Ninjago77/night_light_madness/images/Screenshot 2026-06-29 014659.png

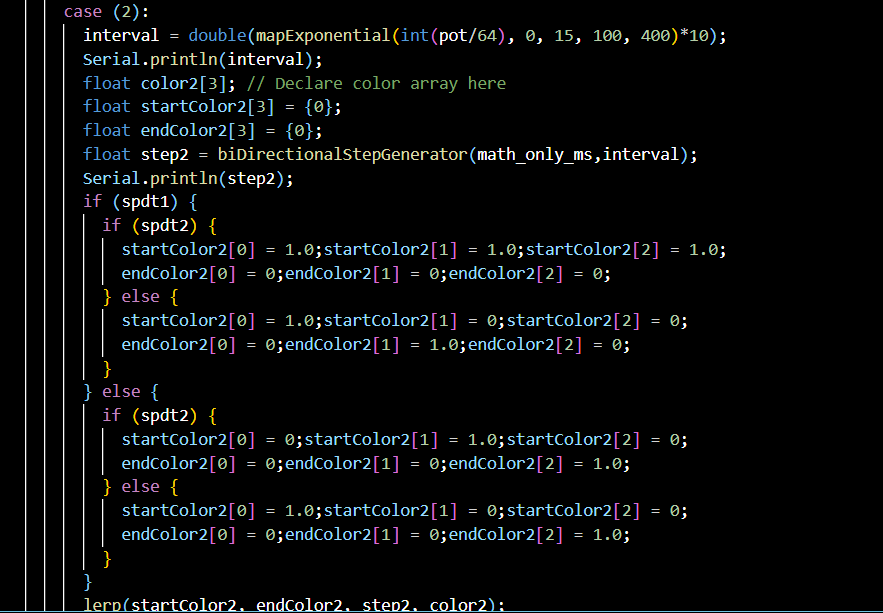
images/Screenshot 2026-06-29 014659.png
