Ninjago77/night_light_madness/images/Screenshot 2026-06-29 015512.png

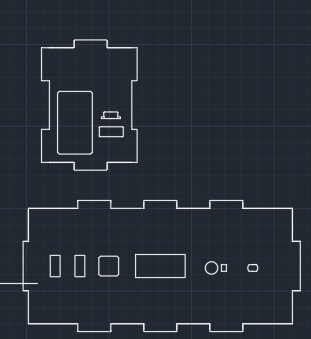
images/Screenshot 2026-06-29 015512.png
