Ninjago77/night_light_madness/images/WhatsApp Image 2026-06-28 at 13.12.44 (2).jpeg

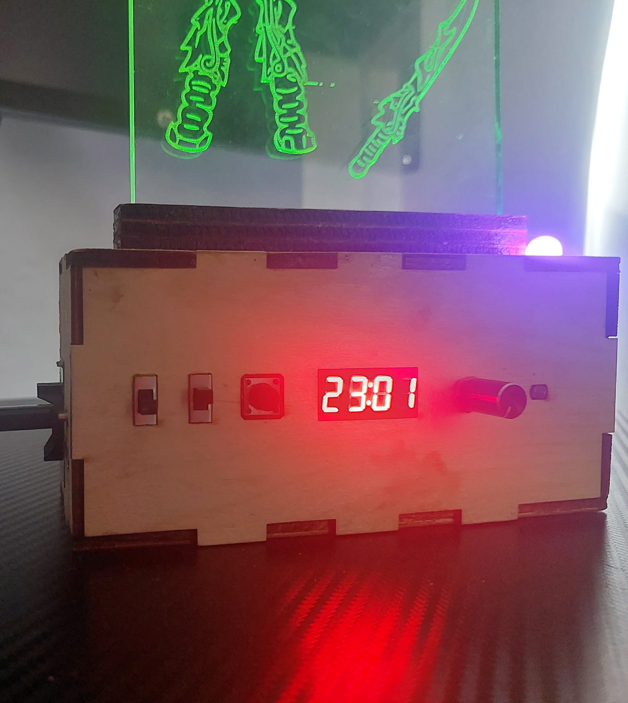
images/WhatsApp Image 2026-06-28 at 13.12.44 (2).jpeg
