Ninjago77/night_light_madness/images/WhatsApp Image 2026-06-28 at 13.21.41.jpeg

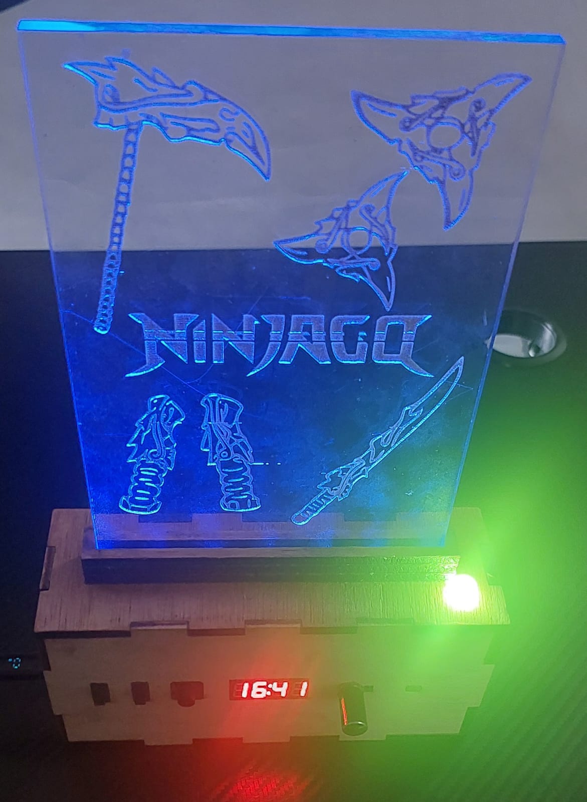
images/WhatsApp Image 2026-06-28 at 13.21.41.jpeg
