Ninjago77/night_light_madness/images/WhatsApp Image 2026-06-29 at 01.42.47 (3).jpeg

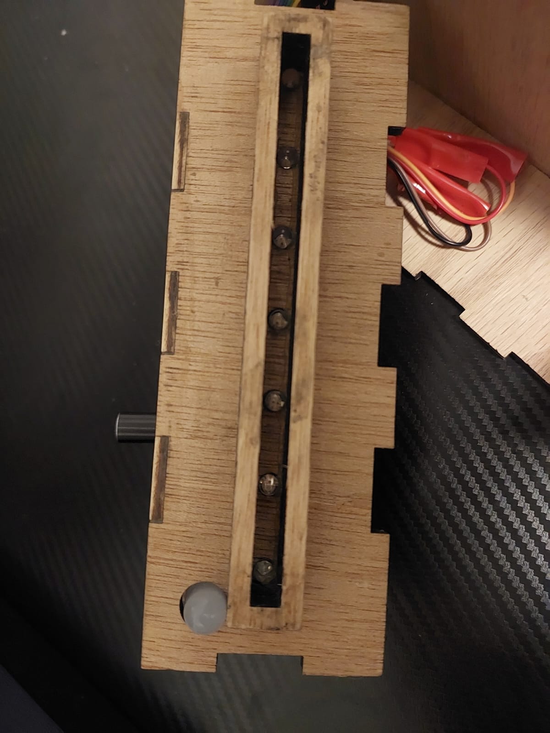
images/WhatsApp Image 2026-06-29 at 01.42.47 (3).jpeg
