Ninjago77/night_light_madness/images/WhatsApp Image 2026-06-29 at 01.42.47 (4).jpeg

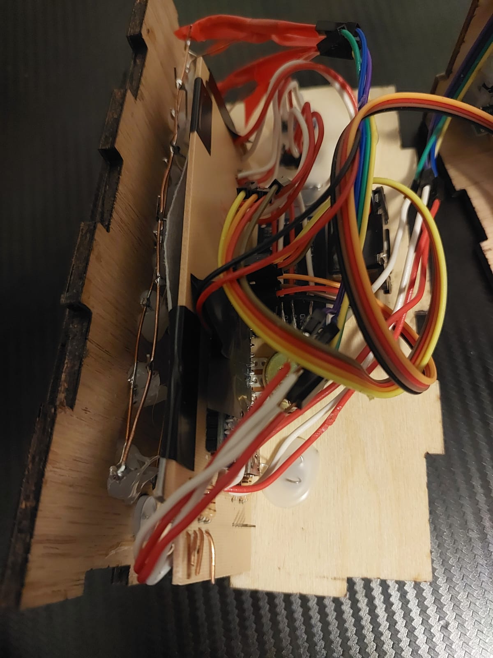
images/WhatsApp Image 2026-06-29 at 01.42.47 (4).jpeg
